yhfudev/smartshow-fluke8050a/software/smartshow-fluke8050a/f8res-digit-lg.h

#ifndef DIGIT_LG_H
#define DIGIT_LG_H

// digit width & height
#define W_DIGIT_LG 40
#define H_DIGIT_LG 80
// dp width & height
#define W_DP_LG 8
#define H_DP_LG 80
 
#define DIGIT_LG(n) (n<10?(uint8_t*)pgm_read_word(&(digit_lg[n])):0)

// 0
const uint8_t digit_lg_0[] PROGMEM = {
  0x00, 0x00, 0xFF, 0x00, 0x00,
  0x00, 0x07, 0xFF, 0xE0, 0x00,
  0x00, 0x0F, 0xFF, 0xF0, 0x00,
  0x00, 0x3F, 0xFF, 0xF8, 0x00,
  0x00, 0x7F, 0xFF, 0xFC, 0x00,
  0x00, 0x7F, 0xFF, 0xFE, 0x00,
  0x00, 0xFF, 0xFF, 0xFF, 0x00,
  0x01, 0xFF, 0xFF, 0xFF, 0x00,
  0x01, 0xFF, 0xFF, 0xFF, 0x80,
  0x01, 0xFF, 0xC3, 0xFF, 0x80,
  0x03, 0xFF, 0x81, 0xFF, 0xC0,
  0x03, 0xFF, 0x00, 0xFF, 0xC0,
  0x03, 0xFE, 0x00, 0x7F, 0xC0,
  0x07, 0xFE, 0x00, 0x7F, 0xE0,
  0x07, 0xFE, 0x00, 0x7F, 0xE0,
  0x07, 0xFC, 0x00, 0x3F, 0xE0,
  0x07, 0xFC, 0x00, 0x3F, 0xE0,
  0x0F, 0xFC, 0x00, 0x3F, 0xF0,
  0x0F, 0xFC, 0x00, 0x3F, 0xF0,
  0x0F, 0xFC, 0x00, 0x3F, 0xF0,
  0x0F, 0xFC, 0x00, 0x3F, 0xF0,
  0x0F, 0xFC, 0x00, 0x3F, 0xF0,
  0x0F, 0xF8, 0x00, 0x3F, 0xF0,
  0x0F, 0xF8, 0x00, 0x1F, 0xF0,
  0x0F, 0xF8, 0x00, 0x1F, 0xF0,
  0x1F, 0xF8, 0x00, 0x1F, 0xF8,
  0x1F, 0xF8, 0x00, 0x1F, 0xF8,
  0x1F, 0xF8, 0x00, 0x1F, 0xF8,
  0x1F, 0xF8, 0x00, 0x1F, 0xF8,
  0x1F, 0xF8, 0x00, 0x1F, 0xF8,
  0x1F, 0xF8, 0x00, 0x1F, 0xF8,
  0x1F, 0xF8, 0x00, 0x1F, 0xF8,
  0x1F, 0xF8, 0x00, 0x1F, 0xF8,
  0x1F, 0xF8, 0x00, 0x1F, 0xF8,
  0x1F, 0xF8, 0x00, 0x1F, 0xF8,
  0x1F, 0xF8, 0x00, 0x1F, 0xF8,
  0x1F, 0xF8, 0x00, 0x1F, 0xF8,
  0x1F, 0xF8, 0x00, 0x1F, 0xF8,
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
  0x00,
  0x00,
  0x00,
  0x00,
  0x00,
  0x00,
  0x00,
  0x00,
  0x00,
  0x00,
  0x00,
  0x00,
  0x00,
  0x00,
  0x00,
  0x00,
  0x00,
  0x00,
  0x00,
  0x00,
  0x00,
  0x00,
  0x00,
  0x00,
  0x00,
  0x00,
  0x00,
  0x00,
  0x00,
  0x00,
  0x00,
  0x00,
  0x00,
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
};

#endif // DIGIT_LG_H
