yhfudev/smartshow-fluke8050a/software/smartshow-fluke8050a/f8res-symbol-unit.h

#ifndef SYMBOLUNIT_H
#define SYMBOLUNIT_H

// bmp width & height
#define W_UNIT 56
#define H_UNIT 41
#define W_UNIT_SM 24
#define H_UNIT_SM 21
// y offset from Y_DIGIT_LG
#define OFFSET_UNIT_LG 46
// y offset from Y_DIGIT_SM
#define OFFSET_UNIT_SM 16

#define UNIT_LG(n)  (n?(uint8_t*)pgm_read_word(&(symbolUnit[n-1])):UNIT_NONE)
#define UNIT_SM(n)  (n?(uint8_t*)pgm_read_word(&(symbolUnit_sm[n-1])):UNIT_NONE)


  // V
const uint8_t symbolUnit_0[] PROGMEM =
  { 0x3C, 0x03, 0xC0, 0x00, 0x00, 0x00, 0x00,
    0x3C, 0x07, 0x80, 0x00, 0x00, 0x00, 0x00,
    0x3E, 0x07, 0x80, 0x00, 0x00, 0x00, 0x00,
    0x1E, 0x07, 0x80, 0x00, 0x00, 0x00, 0x00,
    0x1E, 0x07, 0x80, 0x00, 0x00, 0x00, 0x00,
    0x1E, 0x07, 0x80, 0x00, 0x00, 0x00, 0x00,
    0x1E, 0x07, 0x00, 0x00, 0x00, 0x00, 0x00,
    0x1E, 0x0F, 0x00, 0x00, 0x00, 0x00, 0x00,
    0x0F, 0x0F, 0x00, 0x00, 0x00, 0x00, 0x00,
    0x0F, 0x0F, 0x00, 0x00, 0x00, 0x00, 0x00,
    0x0F, 0x0F, 0x00, 0x00, 0x00, 0x00, 0x00,
    0x0F, 0x0E, 0x00, 0x00, 0x00, 0x00, 0x00,
    0x0F, 0x1E, 0x00, 0x00, 0x00, 0x00, 0x00,
    0x0F, 0x1E, 0x00, 0x00, 0x00, 0x00, 0x00,
    0x07, 0x1E, 0x00, 0x00, 0x00, 0x00, 0x00,
    0x07, 0x9E, 0x00, 0x00, 0x00, 0x00, 0x00,
    0x07, 0x9C, 0x00, 0x00, 0x00, 0x00, 0x00,
    0x07, 0x9C, 0x00, 0x00, 0x00, 0x00, 0x00,
    0x07, 0x9C, 0x00, 0x00, 0x00, 0x00, 0x00,
    0x03, 0xBC, 0x00, 0x00, 0x00, 0x00, 0x00,
    0x03, 0xBC, 0x00, 0x00, 0x00, 0x00, 0x00,
    0x03, 0xB8, 0x00, 0x00, 0x00, 0x00, 0x00,
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
    0x1F, 0x80, 0x00,
    0x3F, 0xC0, 0x00,
    0x70, 0xE0, 0x00,
    0xE0, 0x70, 0x00,
    0xC0, 0x30, 0x00,
    0xC0, 0x30, 0x00,
    0xC0, 0x30, 0x00,
    0xC0, 0x30, 0x00,
    0xC0, 0x33, 0xFC,
    0xC0, 0x33, 0xFC,
    0x60, 0x60, 0x18,
    0x30, 0xC0, 0x30,
    0x10, 0x80, 0x60,
    0xF0, 0xF0, 0x60,
    0xF0, 0xF0, 0xC0,
    0x00, 0x01, 0x80,
    0x00, 0x03, 0xFC,
    0x00, 0x03, 0xFC,
    0x00, 0x00, 0x00,
    0x00, 0x00, 0x00 };

const uint8_t * const symbolUnit_sm[11] PROGMEM = {
  symbolUnit_sm_0,
  symbolUnit_sm_1,
  symbolUnit_sm_2,
  symbolUnit_sm_3,
  symbolUnit_sm_4,
  symbolUnit_sm_5,
  symbolUnit_sm_6,
  symbolUnit_sm_7,
  symbolUnit_sm_8,
  symbolUnit_sm_9,
  symbolUnit_sm_10
};

#endif // SYMBOLUNIT_H
