yhfudev/smartshow-fluke8050a/software/smartshow-fluke8050a/f8res-symbol-mode.h

#ifndef SYMBOLMODE_H
#define SYMBOLMODE_H

// bmp width & height
#define W_MODE    40
#define H_MODE    32
#define W_MODE_SM 19
#define H_MODE_SM 14
// y offset from Y_DIGIT_LG
#define OFFSET_MODE_LG 0
// y offset from Y_DIGIT_SM
#define OFFSET_MODE_SM 0

#define W_LOBATT  36
#define H_LOBATT  16

#define W_SET_Z   64
#define H_SET_Z   32

#define MODE_LG(n) (n?(uint8_t*)pgm_read_word(&(symbolMode[n-1])):MODE_NONE)
#define MODE_SM(n) (n?(uint8_t*)pgm_read_word(&(symbolMode_sm[n-1])):MODE_NONE)

// DC
const uint8_t symbolMode_0[] PROGMEM = {
  0x00, 0x00, 0x00, 0x00, 0x00,
  0x00, 0x00, 0x00, 0x00, 0x00,
  0x00, 0x3F, 0xE0, 0x00, 0x3E,
  0x00, 0x3F, 0xF0, 0x00, 0xFF,
  0x00, 0x3F, 0xF8, 0x01, 0xFF,
  0x00, 0x3C, 0x7C, 0x03, 0xE1,
  0x00, 0x3C, 0x3E, 0x03, 0xC0,
  0x00, 0x3C, 0x1E, 0x07, 0x80,
  0x00, 0x3C, 0x1E, 0x07, 0x80,
  0x00, 0x3C, 0x1E, 0x07, 0x80,
  0x00, 0x3C, 0x0F, 0x0F, 0x00,
  0x00, 0x3C, 0x0F, 0x0F, 0x00,
  0x00, 0x3C, 0x0F, 0x0F, 0x00,
  0x00, 0x3C, 0x0F, 0x0F, 0x00,
  0x00, 0x3C, 0x0F, 0x0F, 0x00,
  0x00, 0x3C, 0x0F, 0x0F, 0x00,
  0x00, 0x3C, 0x0F, 0x0F, 0x00,
  0x00, 0x3C, 0x0F, 0x0F, 0x00,
  0x00, 0x3C, 0x0F, 0x0F, 0x00,
  0x00, 0x3C, 0x0F, 0x0F, 0x00,
  0x00, 0x3C, 0x0F, 0x0F, 0x00,
  0x00, 0x3C, 0x0F, 0x0F, 0x00,
  0x00, 0x3C, 0x0F, 0x0F, 0x00,
  0x00, 0x3C, 0x0E, 0x07, 0x80,
  0x00, 0x3C, 0x1E, 0x07, 0x80,
  0x00, 0x3C, 0x1E, 0x07, 0x80,
  0x00, 0x3C, 0x3E, 0x03, 0xC0,
  0x00, 0x3C, 0x7C, 0x03, 0xE1,
  0x00, 0x3F, 0xF8, 0x01, 0xFF,
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
    0xF1, 0xF0, 0xF0, 0x00, 0x3C, 0x00, 0x1E, 0x00,
    0x7F, 0xE0, 0xFF, 0xE0, 0x3C, 0x00, 0x3F, 0xFE,
    0x3F, 0xC0, 0xFF, 0xE0, 0x3C, 0x00, 0x3F, 0xFE,
    0x1F, 0x80, 0xFF, 0xE0, 0x3C, 0x00, 0x3F, 0xFE,
    0x00, 0x00, 0x00, 0x00, 0x00, 0x00, 0x00, 0x00 };

#endif // SYMBOLMODE_H
